ferrucci-franco/from_galileo_to_arduino/media/ver00/photos/IMG_0405.JPEG

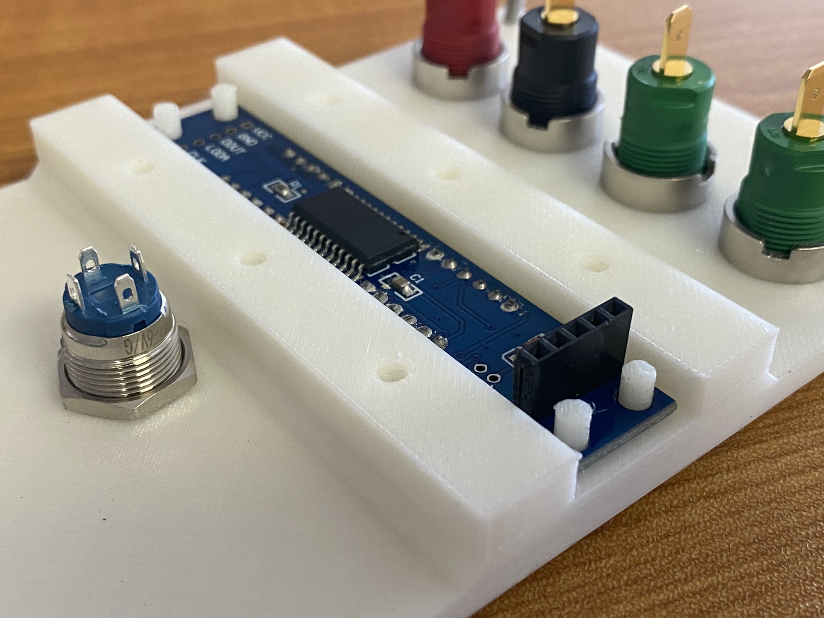
media/ver00/photos/IMG_0405.JPEG
